joaroyen/arcade-kitchen-timer/docs/img/mini-enclosure-top-support.png

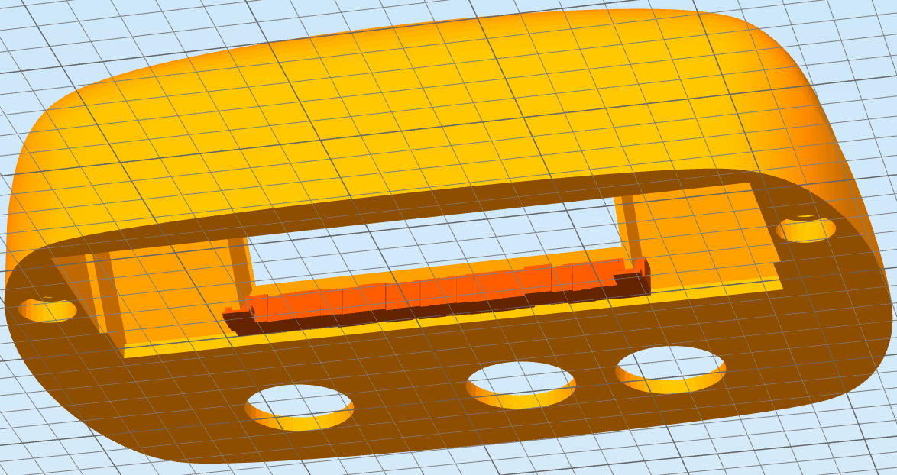
docs/img/mini-enclosure-top-support.png
