joaroyen/arcade-kitchen-timer/docs/img/history-breadboard.jpg

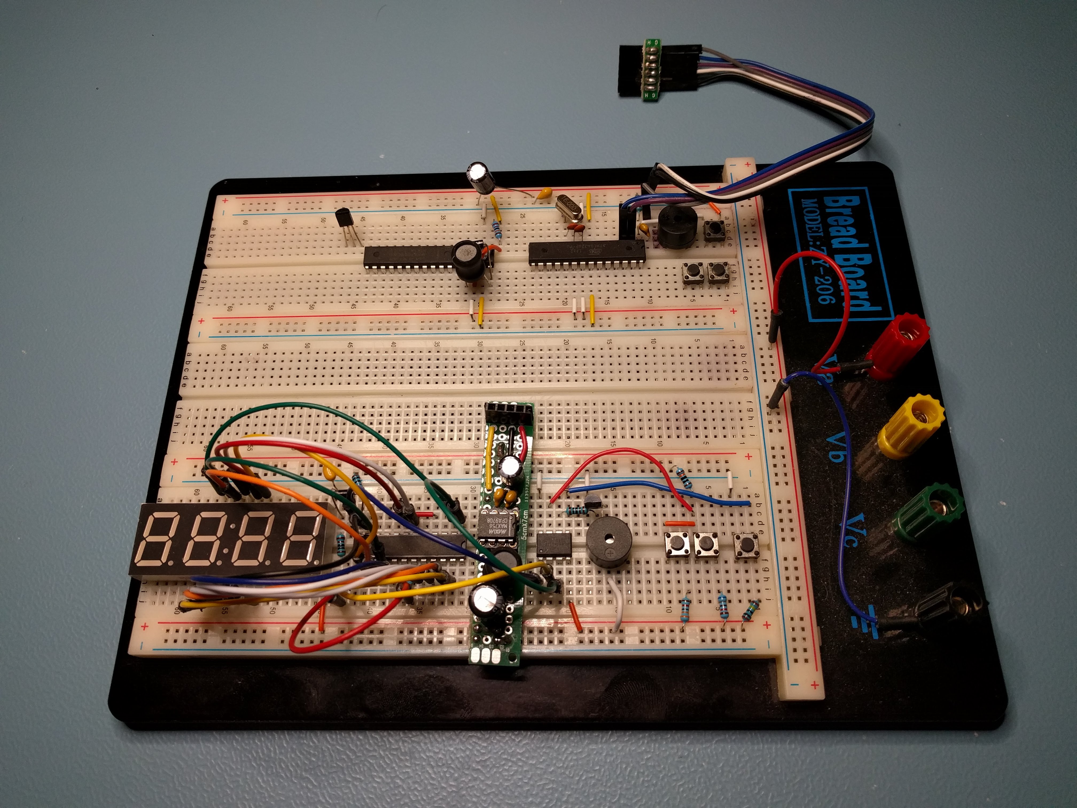
docs/img/history-breadboard.jpg
