joaroyen/arcade-kitchen-timer/docs/img/history-pcb-rev01.jpg

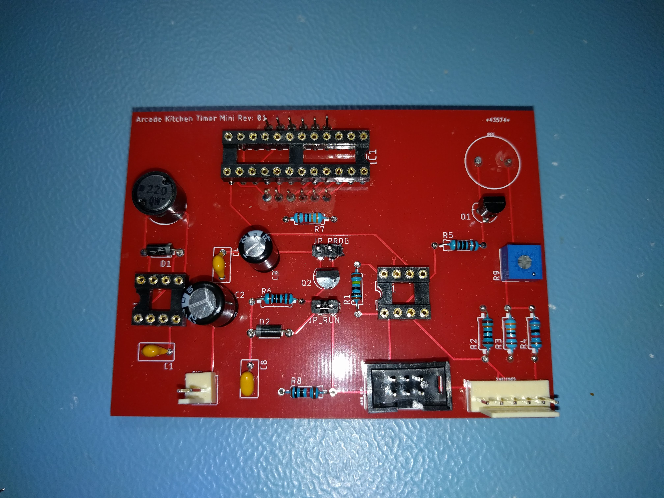
docs/img/history-pcb-rev01.jpg
