joaroyen/arcade-kitchen-timer/docs/img/history-protoboard.jpg

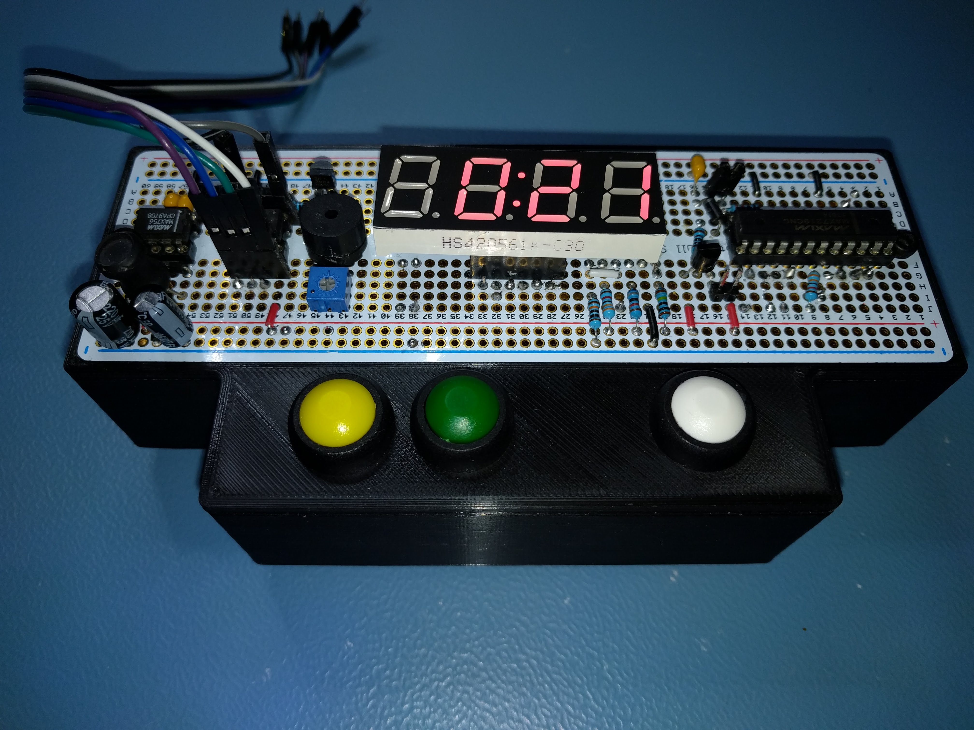
docs/img/history-protoboard.jpg
