joaroyen/arcade-kitchen-timer/docs/img/issue-display-ghosting.png

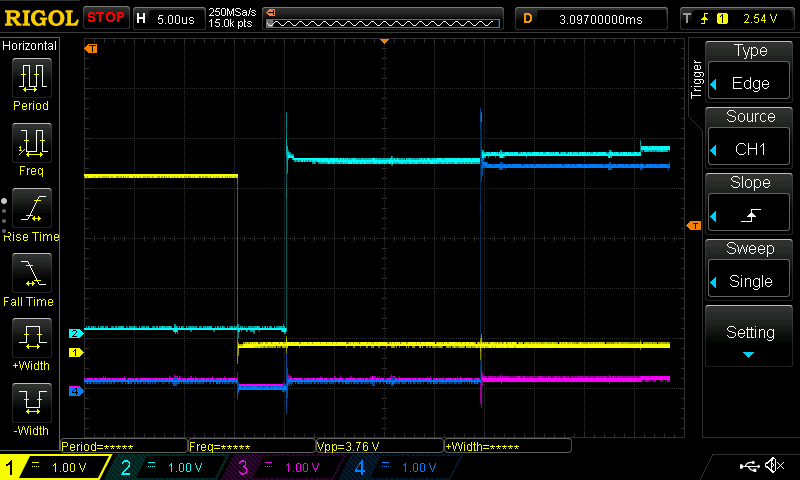
docs/img/issue-display-ghosting.png
