joaroyen/arcade-kitchen-timer/docs/img/issue-display-no-ghosting.png

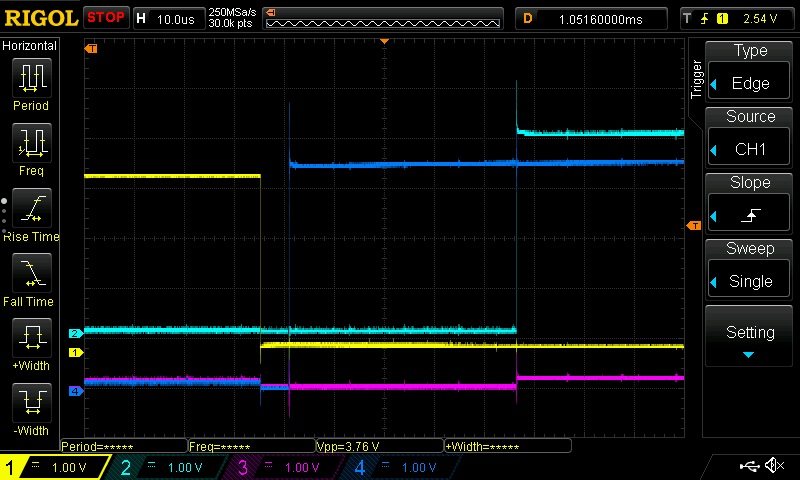
docs/img/issue-display-no-ghosting.png
